Celnardur/rfc_tackle_sensor/Releases/REV0.1_12_1_2022/tackle_sensor_hardware.pdf

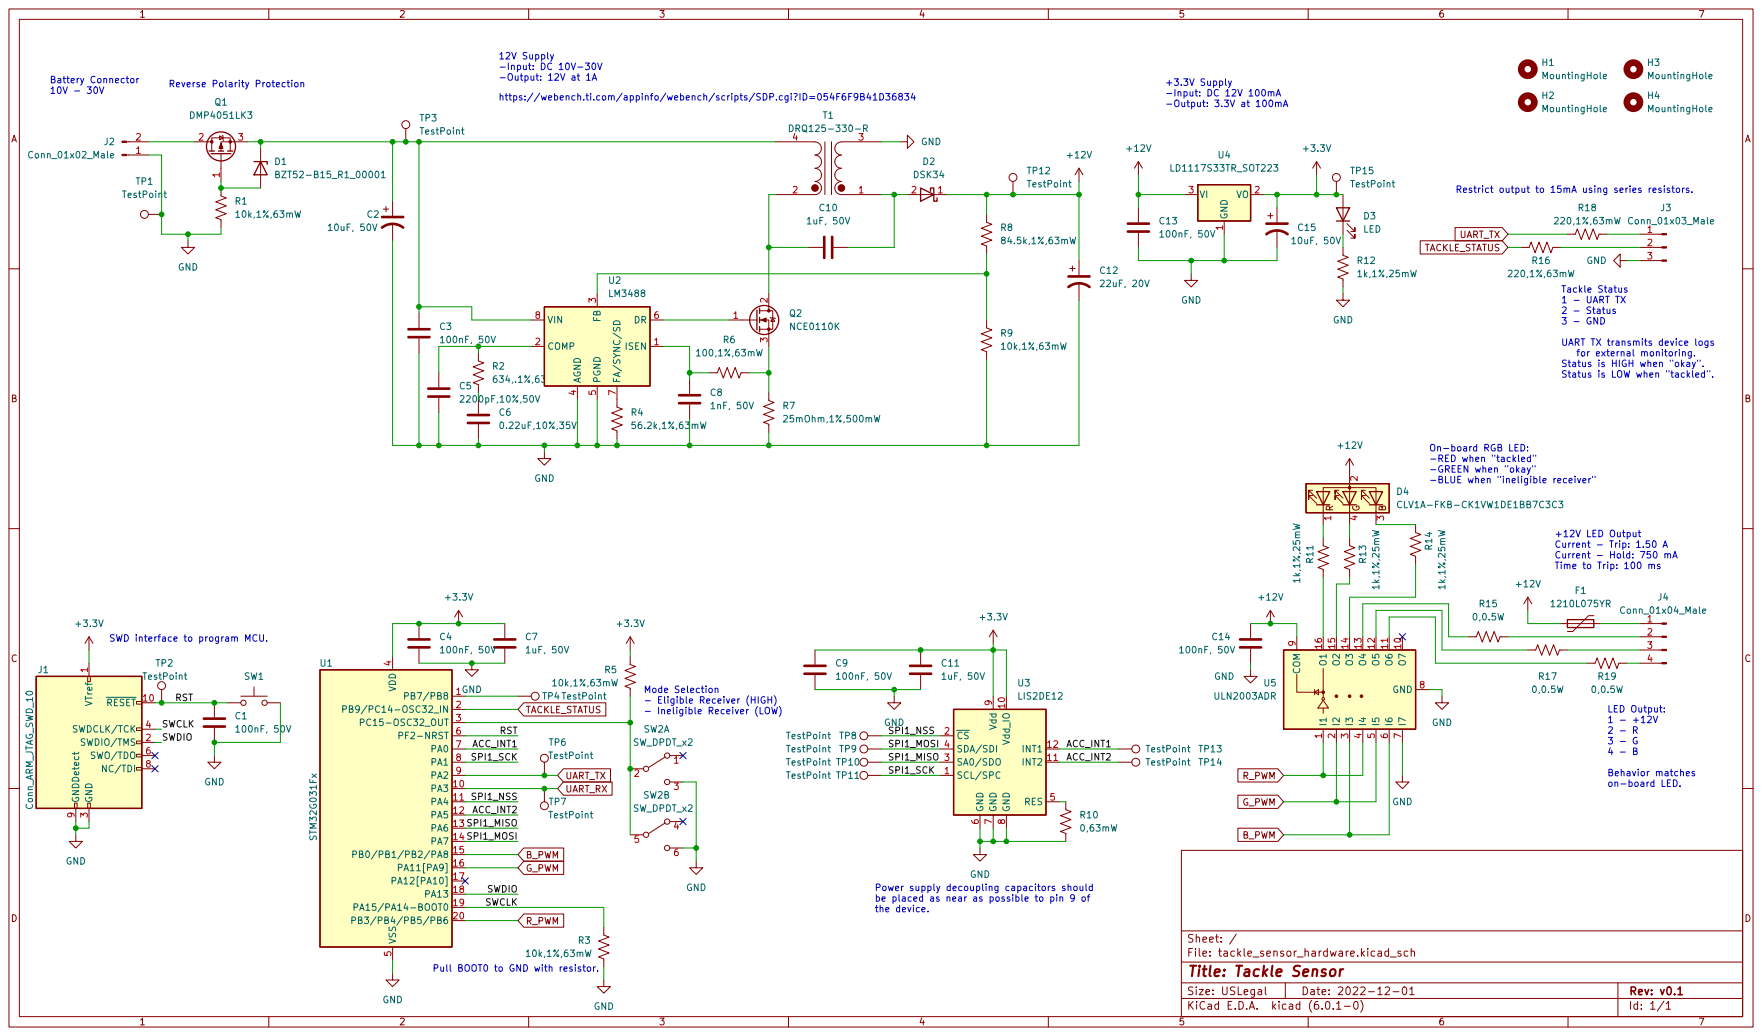
[picture p7: page 1]

12V Supply
-Input: DC 10V-30V
-Output: 12V at 1A
https://webench.ti.com/appinfo/webench/scripts/SDP.cgi?ID=054F6F9B41D36834

Status is HIGH when "okay". Status is LOW when "tackled". Restrict output to 15mA using series resistors.

Tackle Status 1 - UART TX

5 DR 6 FA/SYNC/SD

UART TX transmits device logs
for external monitoring.

On-board RGB LED: -RED when "tackled"

-GREEN when "okay"
-BLUE when "ineligible receiver"

+12V LED Output
Current - Trip: 1.50 A Current - Hold: 750 mA

Time to Trip: 100 ms

SWD interface to program MCU.

the device. Mode Selection
- Eligible Receiver (HIGH)

3 SWDCLK/TCK 4 SWO/TDO 6 NC/TDI 8 GNDDetect 9

Behavior matches on-board LED.

Power supply decoupling capacitors should
be placed as near as possible to pin 9 of

D Date: 2022-12-01 KiCad E.D.A. kicad (6.0.1-0)
File: tackle_sensor_hardware.kicad_sch Sheet: /
Id: 1/1 Title: Tackle Sensor

Pull BOOT0 to GND with resistor.
