Celnardur/rfc_tackle_sensor/Releases/REV1_08_31_2023/tackle_sensor_hardware-F_Silkscreen.pdf

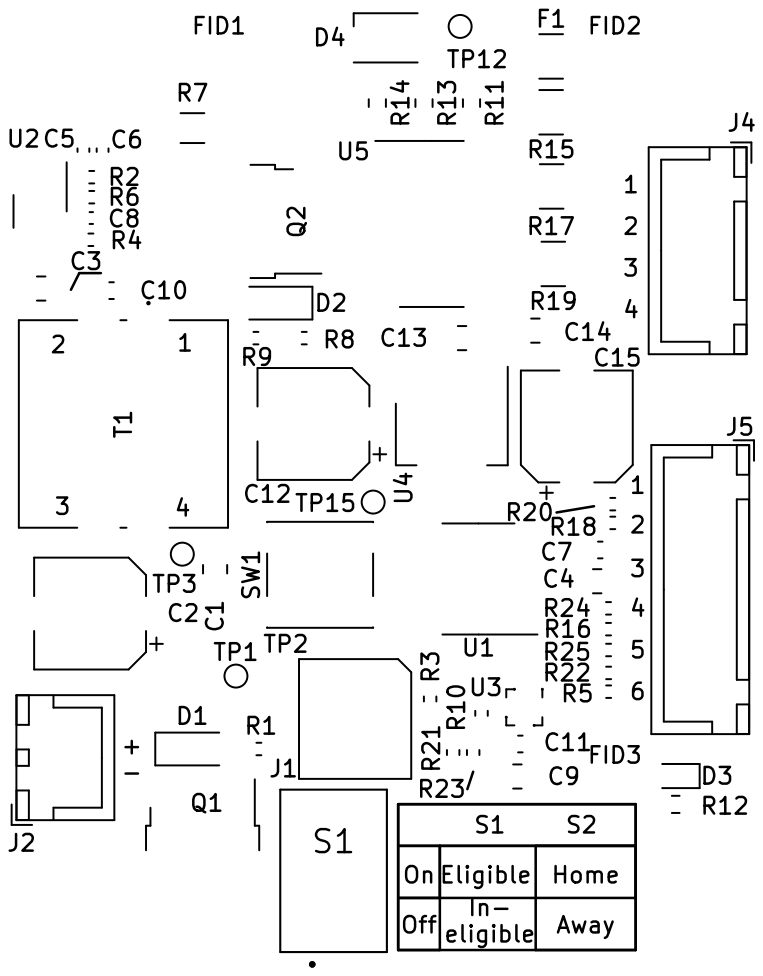
[picture p17: page 1]
