Celnardur/rfc_tackle_sensor/Releases/REV1_08_31_2023/tackle_sensor_hardware-In1_Cu.pdf

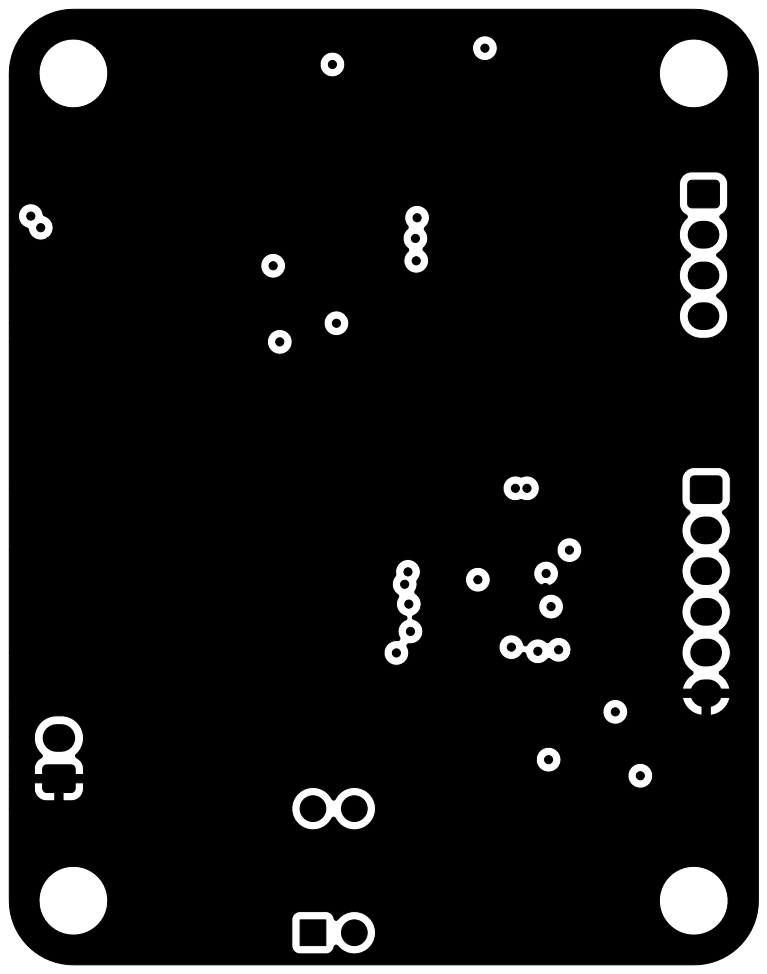
[picture p18: page 1]
