Celnardur/rfc_tackle_sensor/Releases/REV1_08_31_2023/tackle_sensor_hardware-In2_Cu.pdf

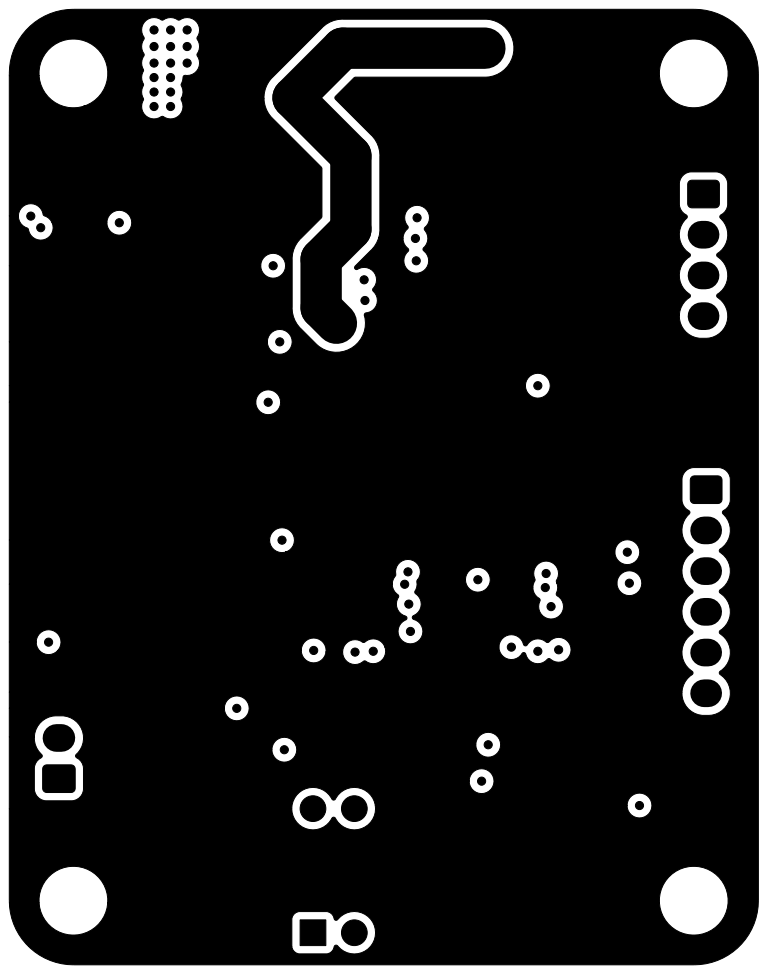
[picture p19: page 1]
