Celnardur/rfc_tackle_sensor/Releases/REV2_02_04_2024/reference_sheet_rev2.pdf

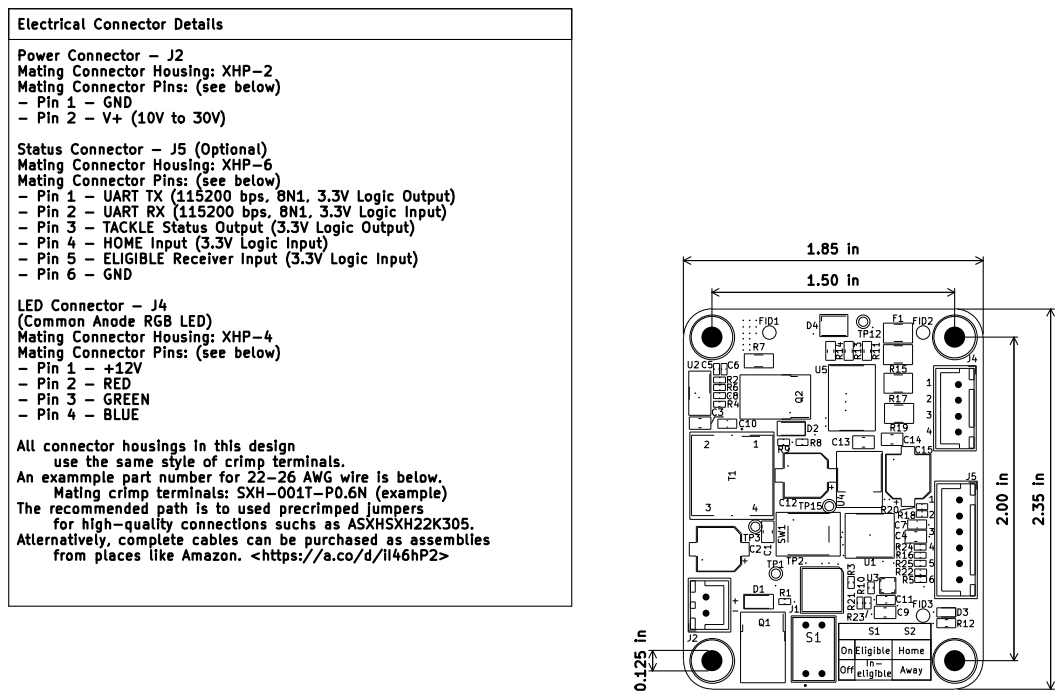
[picture p20: page 1]
