Celnardur/rfc_tackle_sensor/Releases/REV1_08_31_2023/reference_sheet_rev1.pdf

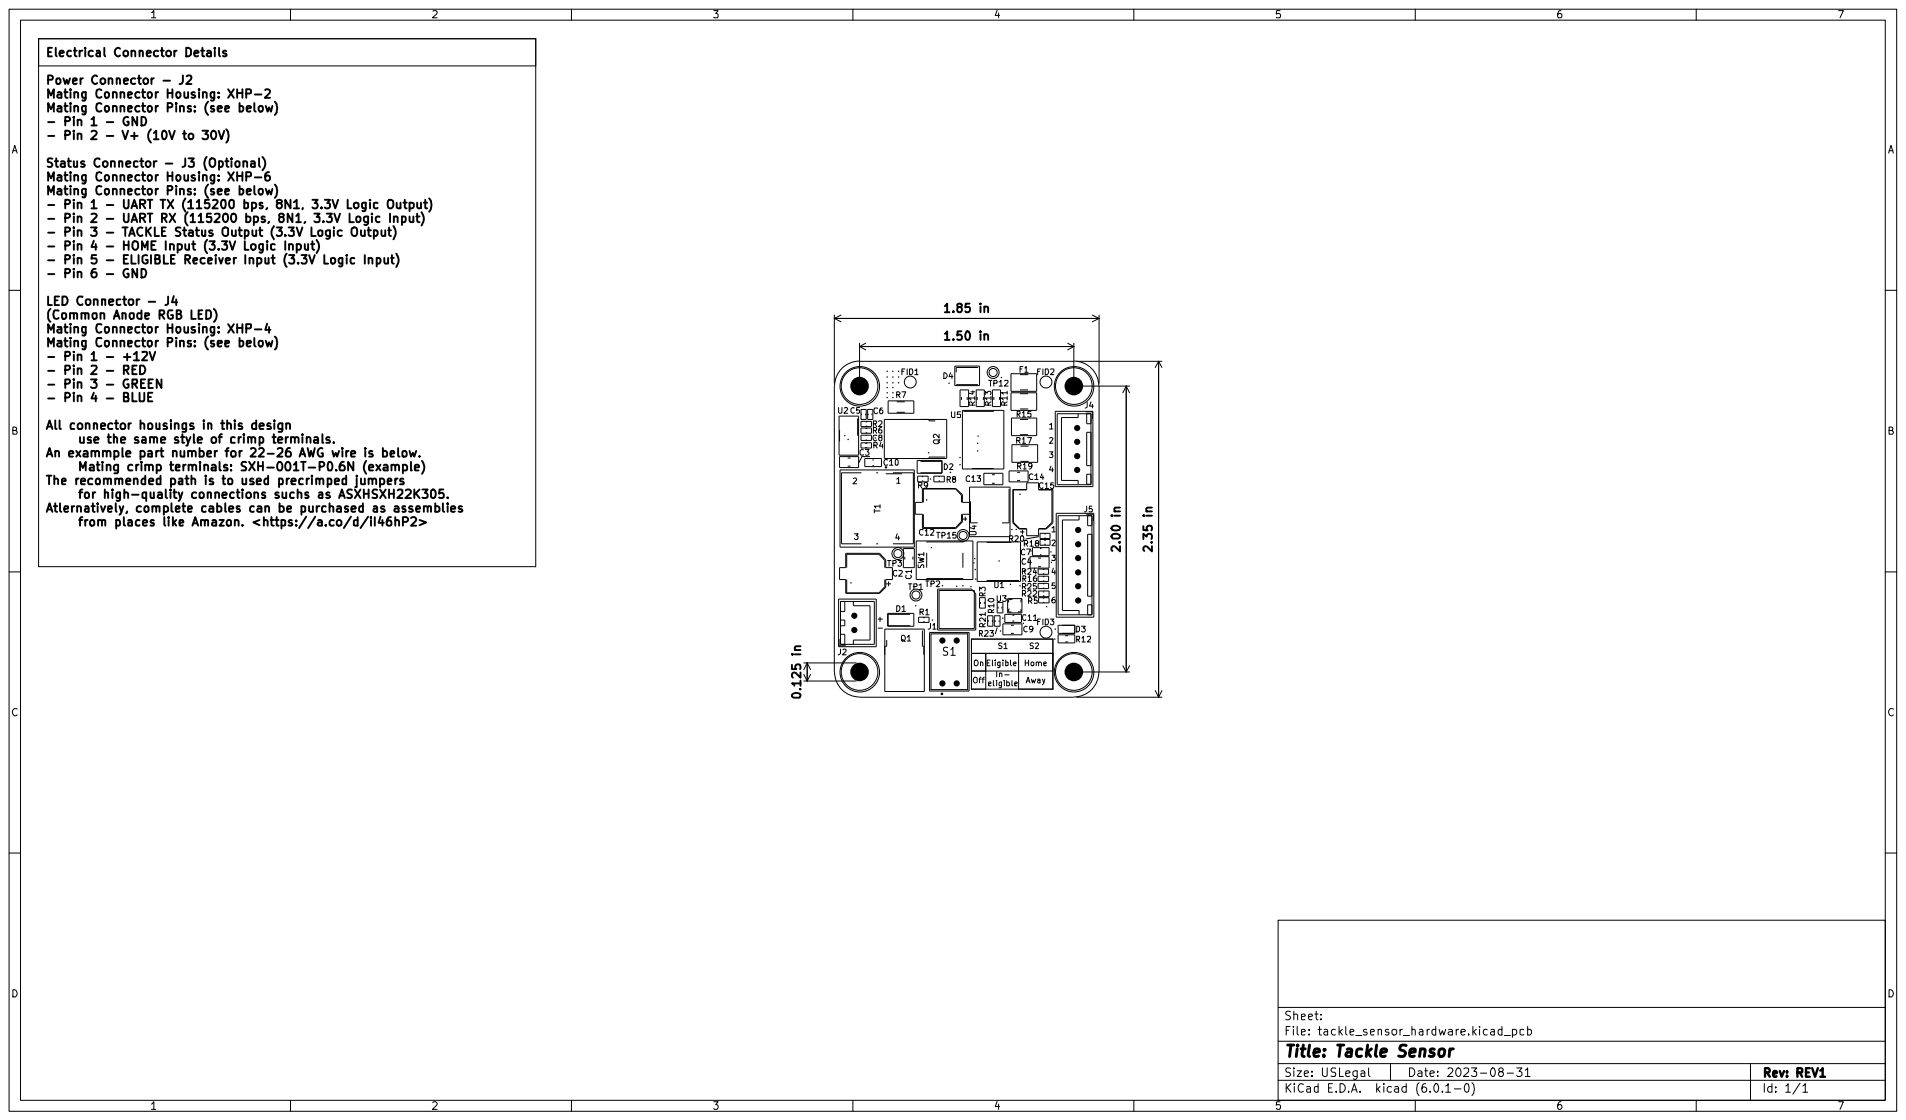
[picture p21: page 1]
